custom-ds/ptSolar/ptSolar/v1.2.0/pcb.pdf

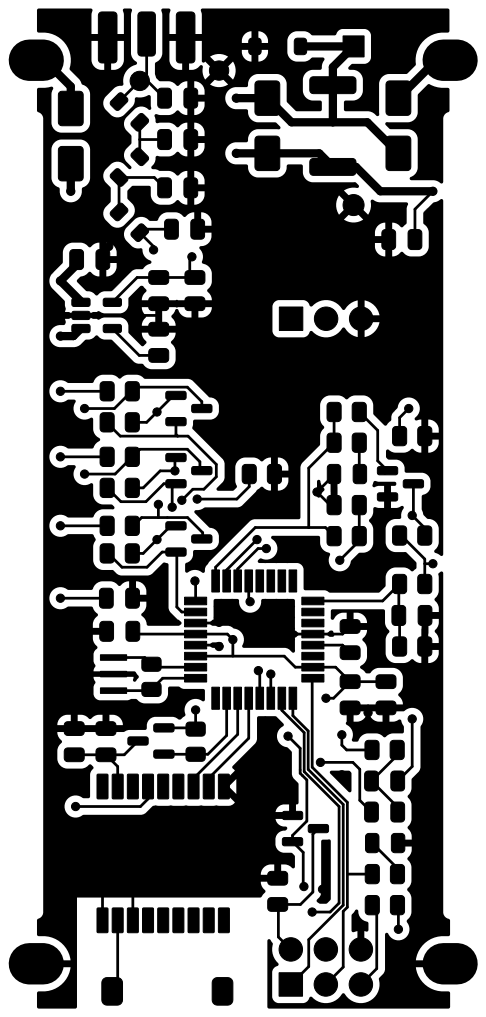
[picture p37: page 1]




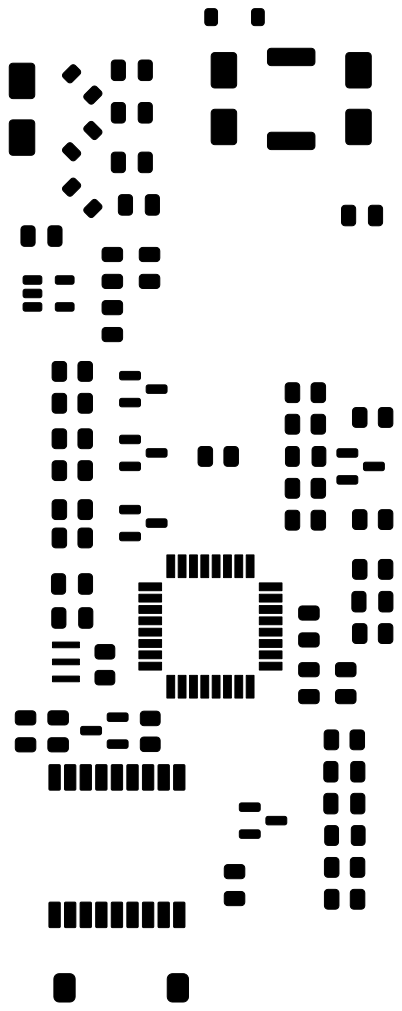
[picture p38: page 5]


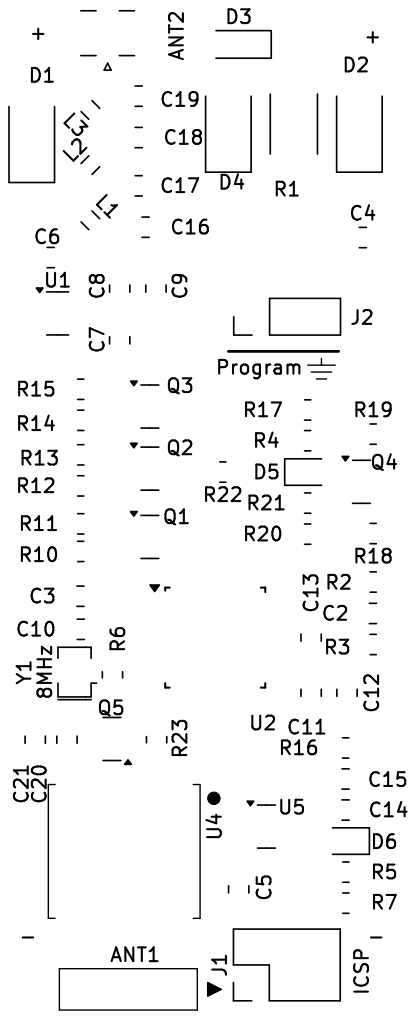
[picture p39: page 7]

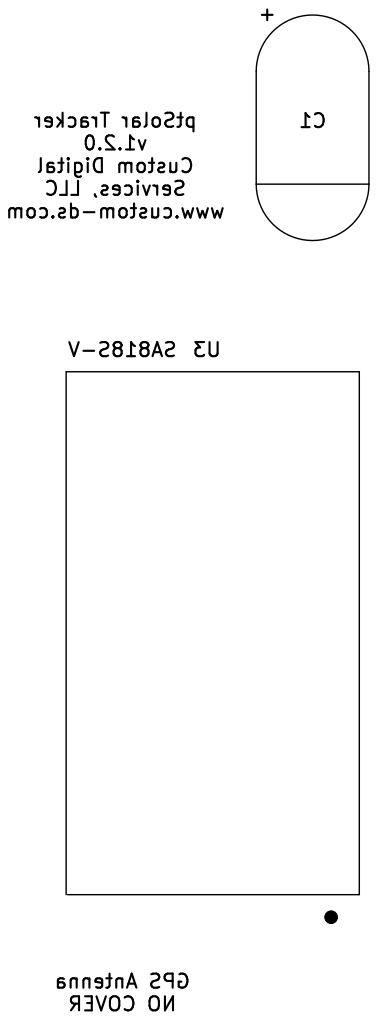
[picture p40: page 8]

LLC Services, www.custom-ds.com

Antenna GPS COVER NO

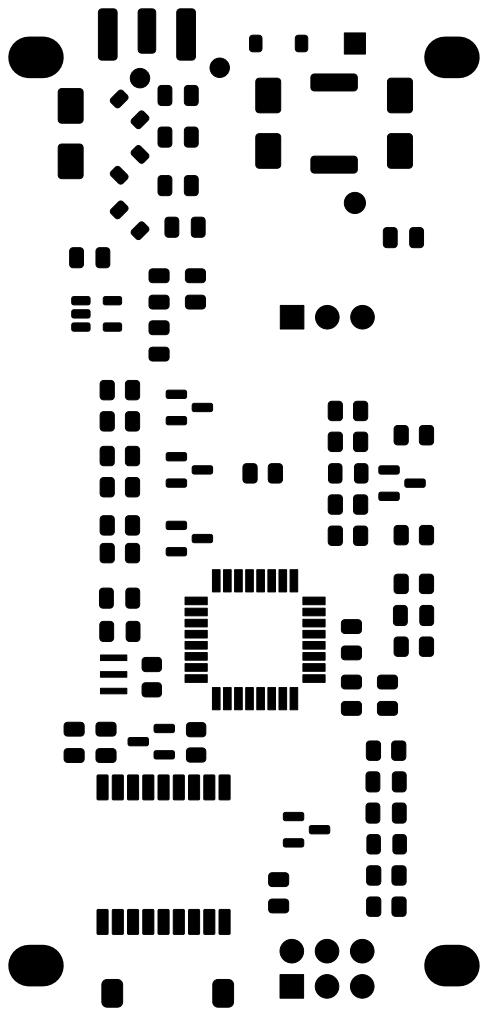
[picture p41: page 9]
