custom-ds/ptSolar/ptSolar/v1.1.0/pcb.pdf

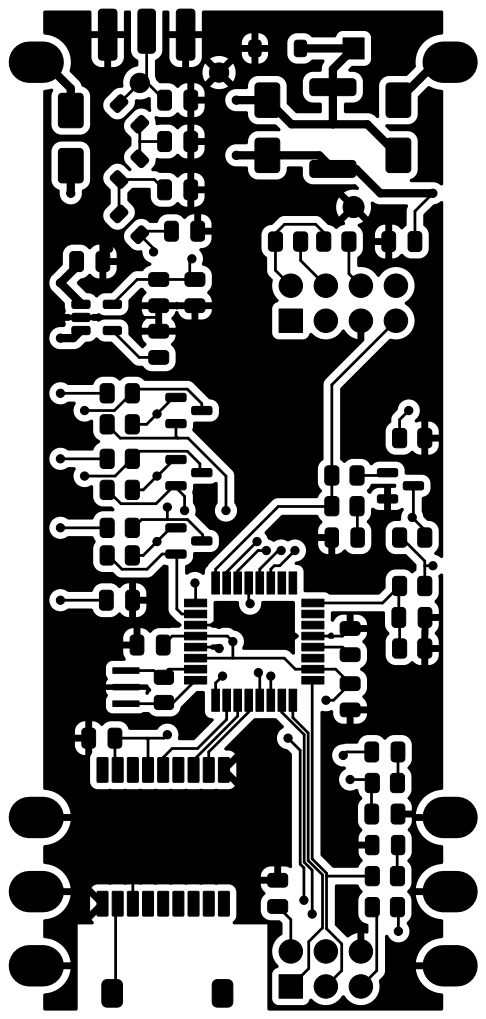
[picture p42: page 1]

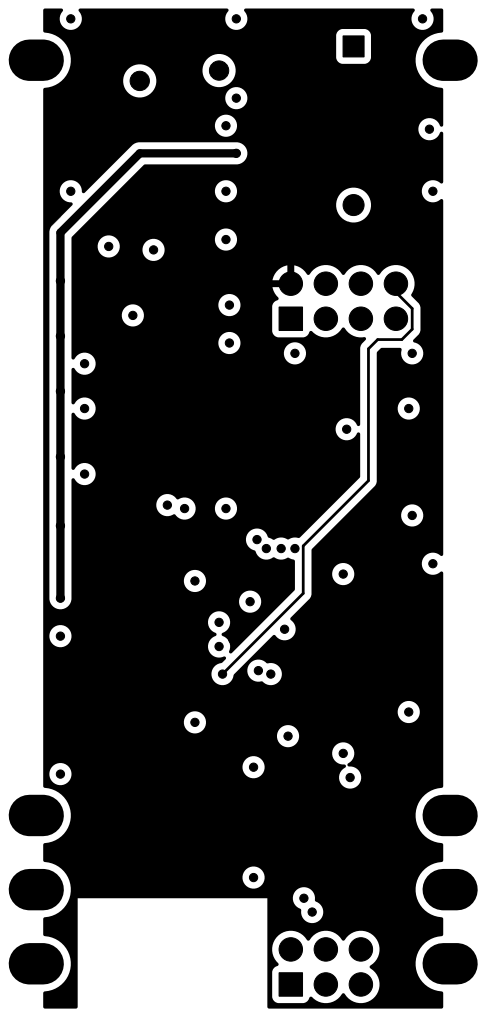
[picture p43: page 2]

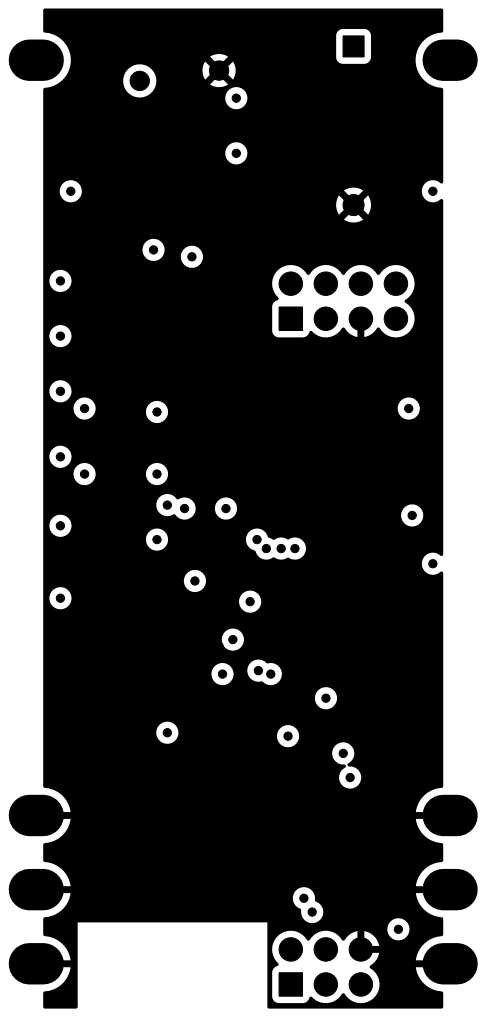
[picture p44: page 3]

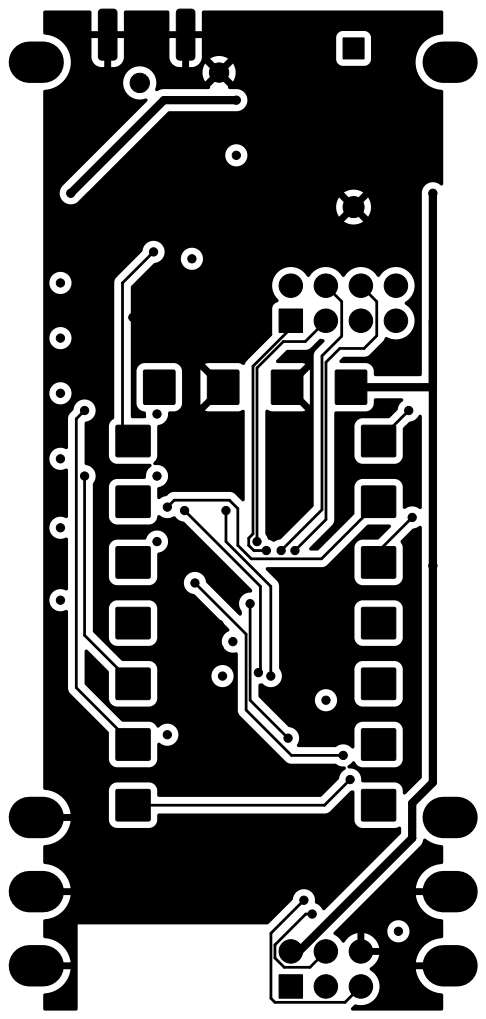
[picture p45: page 4]

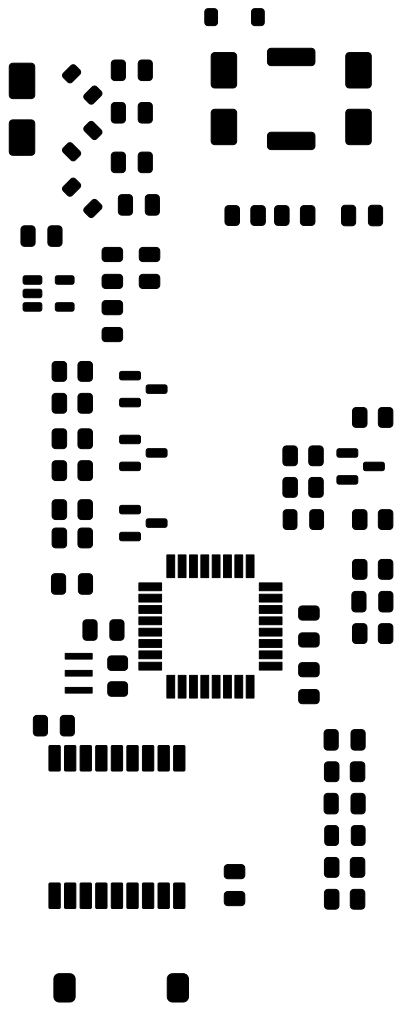
[picture p46: page 5]


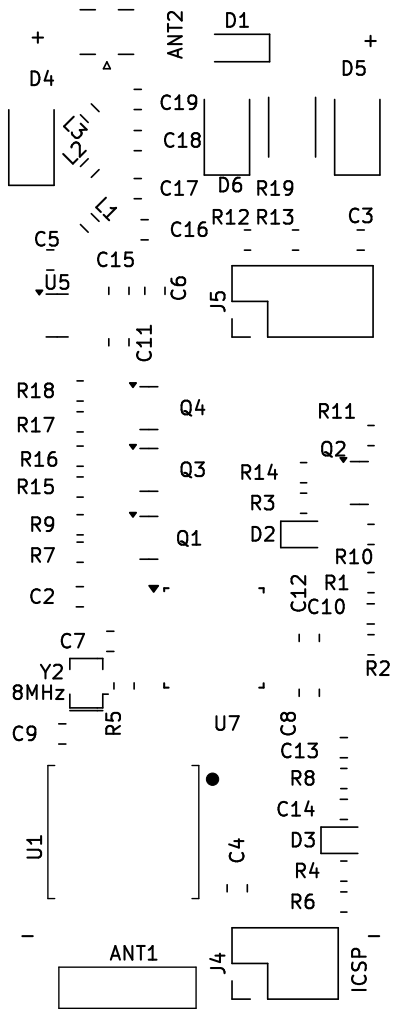
[picture p47: page 7]

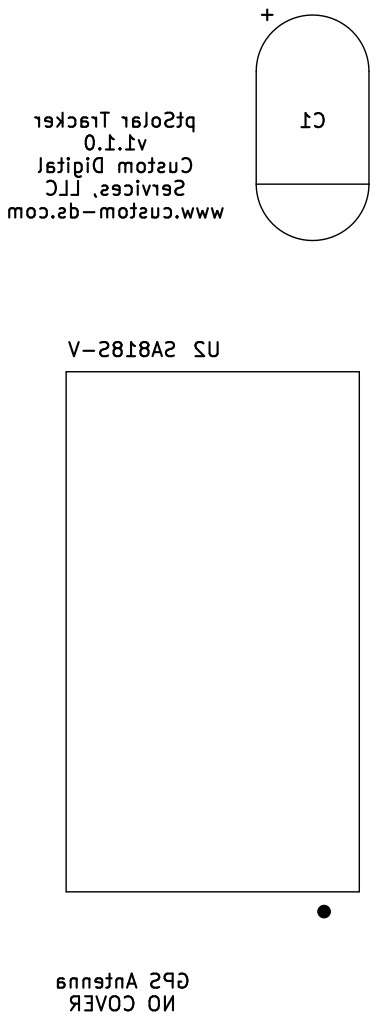
[picture p48: page 8]

LLC Services, www.custom-ds.com

Antenna GPS COVER NO

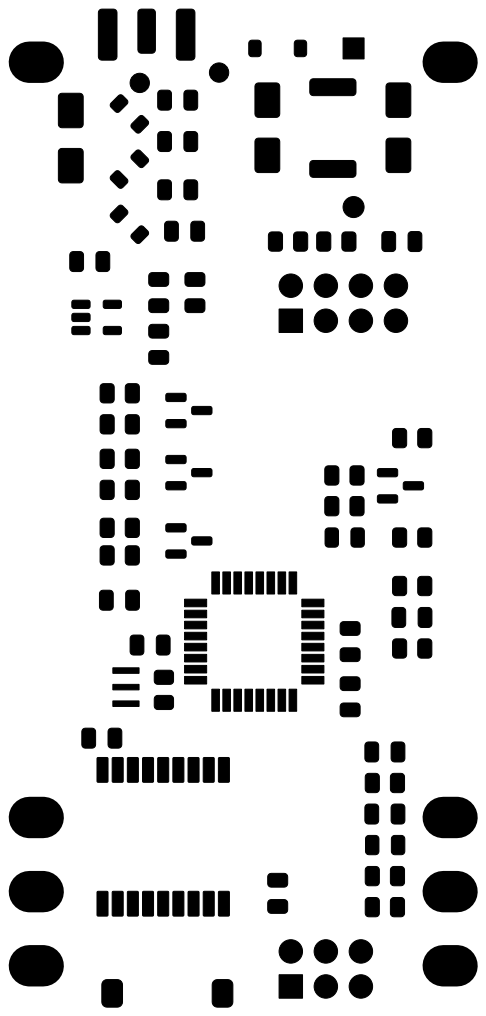
[picture p49: page 9]

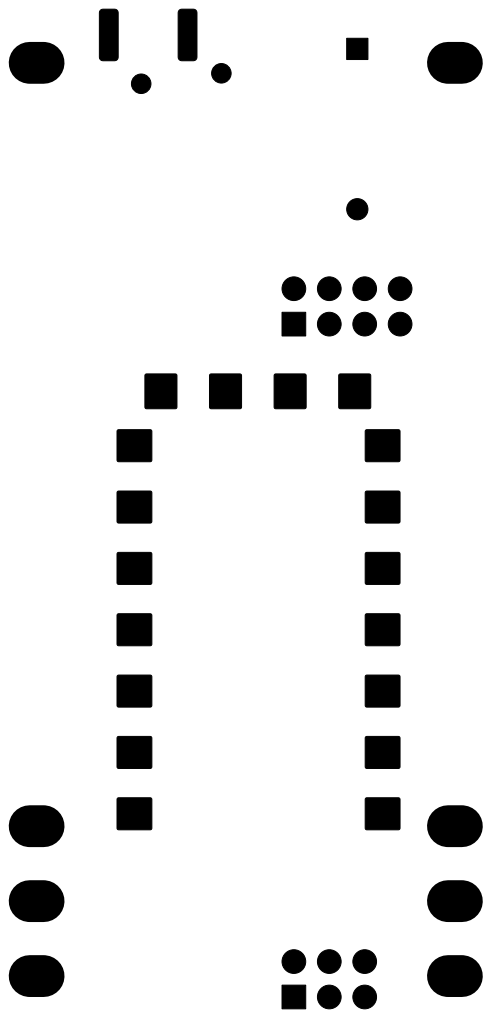
[picture p50: page 10]
