custom-ds/ptSolar/ptSolar/v1.1.1/pcb.pdf

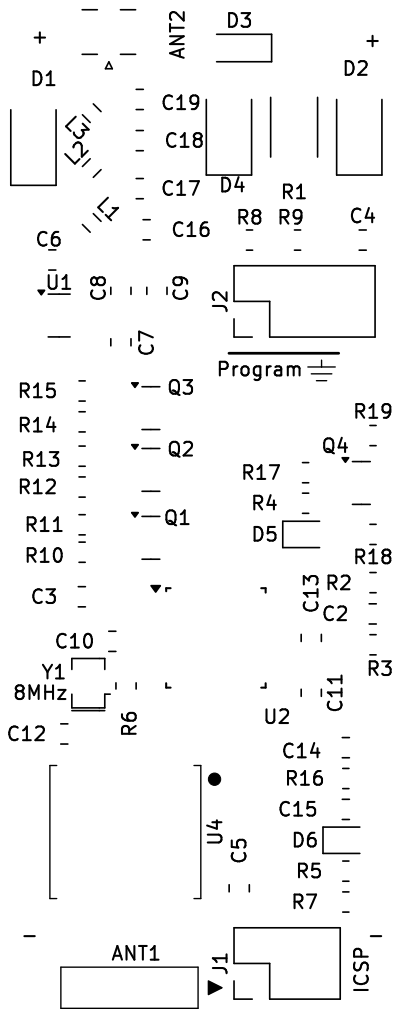
[picture p51: page 7]

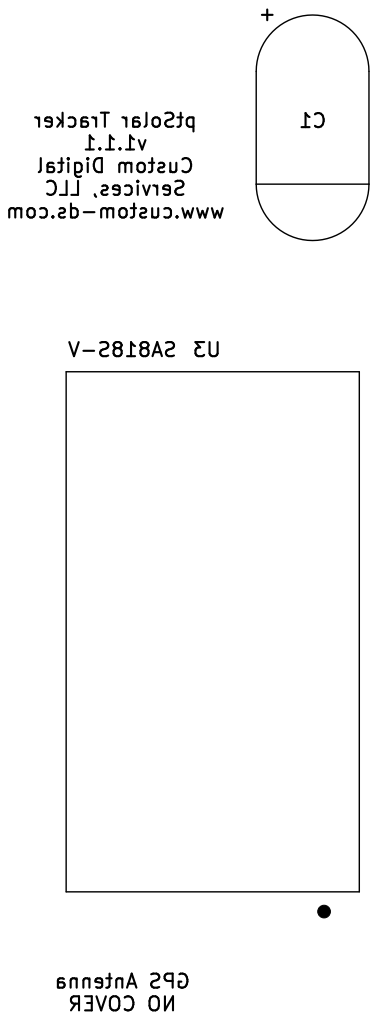
[picture p52: page 8]

LLC Services, www.custom-ds.com

Antenna GPS COVER NO
