custom-ds/ptSolar/firmware/ptSolar/Modem.h

/*
APRS Data Modem for Project: Traveler Flight Controllers
Copyright 2011-2026 - Zack Clobes (W0ZC), Custom Digital Services, LLC

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
You should have received a copy of the GNU General Public License along with this program.  If not, see <http://www.gnu.org/licenses/>.
*/

#ifndef Modem_h
#define Modem_h

#include "BoardDef.h"


#include <stdint.h>   //standard data types available, such as uint8_t
#include <avr/io.h>
#include <avr/interrupt.h>
#include <arduino.h>
#include <avr/wdt.h>

// defines for setting and clearing register bits
#ifndef cbi
#define cbi(sfr, bit) (_SFR_BYTE(sfr) &= ~_BV(bit))
#endif
#ifndef sbi
#define sbi(sfr, bit) (_SFR_BYTE(sfr) |= _BV(bit))
#endif

const uint8_t arySin[] PROGMEM = {2, 5, 7, 10, 12, 15, 17, 20, 22, 24, 
  27, 29, 31, 34, 36, 38, 41, 43, 45, 47, 
  49, 51, 53, 56, 58, 60, 62, 63, 65, 67, 
  69, 71, 72, 74, 76, 77, 79, 80, 82, 83, 
  84, 86, 87, 88, 89, 90, 91, 92, 93, 94, 
  95, 96, 96, 97, 98, 98, 99, 99, 99, 100, 
  100, 100, 100, 100, 100, 100, 100, 100, 99, 99, 
  99, 98, 98, 97, 96, 96, 95, 94, 93, 92, 
  91, 90, 89, 88, 87, 86, 84, 83, 82, 80, 
  79, 77, 76, 74, 72, 71, 69, 67, 65, 63, 
  62, 60, 58, 56, 53, 51, 49, 47, 45, 43, 
  41, 38, 36, 34, 31, 29, 27, 24, 22, 20, 
  17, 15, 12, 10, 7, 5, 2, 0};
  

//Maximum size of the transmit buffer
#define MAX_SZXMIT_SIZE 200

//Maximum time to wait for a response from the radio transmitter module (in milliseconds)245
#define MAX_WAIT_TIMEOUT 2000

//mS Delay when performaing dianostics test transmission
#define DIAGNOSTIC_DELAY 1500


class Modem {
  public:
    // Constructor
    Modem(uint8_t pinEnable, uint8_t pinPTT, uint8_t pinTxAudio, uint8_t pinSerialTx, uint8_t pinSerialRx);

    // Public Functions
    void PTT(bool tx);

    void setTxFrequency(char *szFreq) { strcpy(this->_szTxFreq, szFreq); }
    void setRxFrequency(char *szFreq) { strcpy(this->_szRxFreq, szFreq); }

    void packetHeader(char *szDest, char destSSID, char *szCall, char callSSID, char *szPath1, char path1SSID, char *szPath2, char path2SSID, bool usePath);
    void packetAppend(char *sz);
    void packetAppend(char c);
    void packetAppend(float f);
    void packetAppend(long lNumToSend, bool bLeadingZero);
    void packetSend();

    void sendTestDiagnotics();

    uint8_t getNextBit();       //Called from the ISR routine. Must be public for now
    bool noBitStuffing();    //Called from the ISR routine. Must be public for now

    void setDebugLevel(uint8_t level);
    void setTxDelay(unsigned int txDelay);
    void setCourtesyTone(bool tone) { _courtesyTone = tone; }    //Set the courtesy tone flag

    uint8_t getPinTxAudio();

    inline uint8_t getDACValue(uint8_t iPhase) {
          if (iPhase & 0x80) return 100 + pgm_read_byte(&arySin[(iPhase & 0x7f)]);    //first half of the sine wave
          return 100 - pgm_read_byte(&arySin[(iPhase & 0x7f)]);    //second half of the sine wave
    }
    
    inline unsigned long getLastTransmitMillis() { return _lastTransmitMillis; }
    inline void setLastTransmitMillis() { _lastTransmitMillis = millis(); }    //Set the last transmit time to now


	  //Parameters for the Numerically Controlled Oscillator NCO. See notes in the ConfigureTimers() function for details
    static const uint16_t BAUD_GENERATOR_COUNT = 22;
    static const uint16_t COURTESY_TONE_COUNT = 4000;

    static const uint16_t TONE_HIGH_STEPS_PER_TICK = 5461;		//2200Hz Tone
    static const uint16_t TONE_LOW_STEPS_PER_TICK = 2979; 		//1200Hz Tone
    static const uint16_t TONE_COURTESY_STEPS_PER_TICK = 4220; 		//1700Hz Courtesy Tone

#ifdef TRACKER_PTFLEX
    static const uint16_t TIMER1_OCR = 605;   //606 is the value for a 16MHz clock, which is used by the ptFlex. Shifted down one to account for low-temp operation.
#endif
#ifdef TRACKER_PTSOLAR
    static const uint16_t TIMER1_OCR = 302;    //303 is the value for a 8MHz clock, which is used by the ptSolar that runs at 3.3V. Shifted down one to account for low-temp operation.
#endif


  private:
    // Private Variables
    uint8_t _pinEnable;
    uint8_t _pinPTT;
    uint8_t _pinTxAudio;
    uint8_t _pinSerialTx;
    uint8_t _pinSerialRx;
    unsigned long _lastTransmitMillis;


    uint8_t _debugLevel;

    bool _courtesyTone = false;    //Flag to indicate if the courtesy tone is enabled or not.  This is used to determine if the courtesy tone should be sent or not.

    char _szTxFreq[9];    //array to hold the transmit frequency
    char _szRxFreq[9];    //array to hold the receive frequency


    char _szXmit[MAX_SZXMIT_SIZE];    //array to hold the data to be transmitted
    int _iSZLen;    //Tracks the current size of the szXmit buffer  

    unsigned int _txDelay;
    volatile uint8_t _iSZPos = 0;    //Tracks the current byte being modulated out of the modem
    volatile int _iTxDelayRemaining = 0;
    volatile bool _bNoStuffing = false;
    volatile unsigned int _CRC;
    volatile uint8_t _iTxState = 0;


    // Private Functions
    void calcCRC(bool bit);
    void configTimers();
    void timer1ISR(bool run);

};
#endif
